chenbopeng/Harmonic_GOTO_equator/doc/主控板PCB.jpg

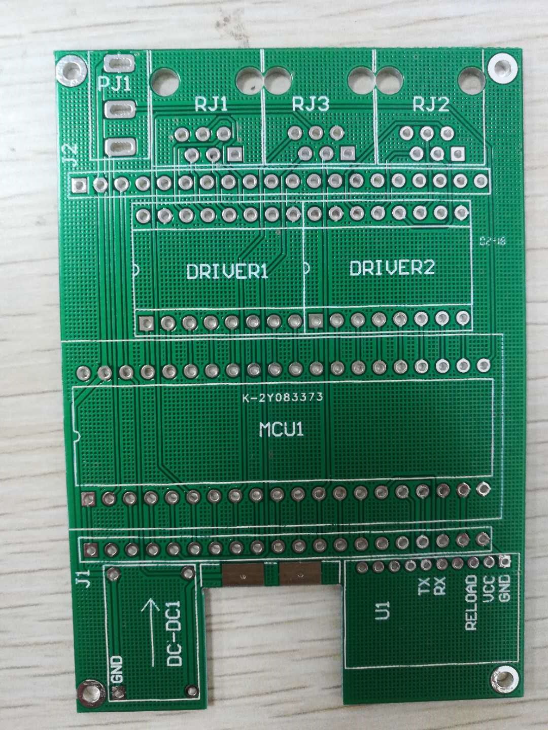
doc/主控板PCB.jpg
