chenbopeng/Harmonic_GOTO_equator/doc/主控板正面 (2).jpg

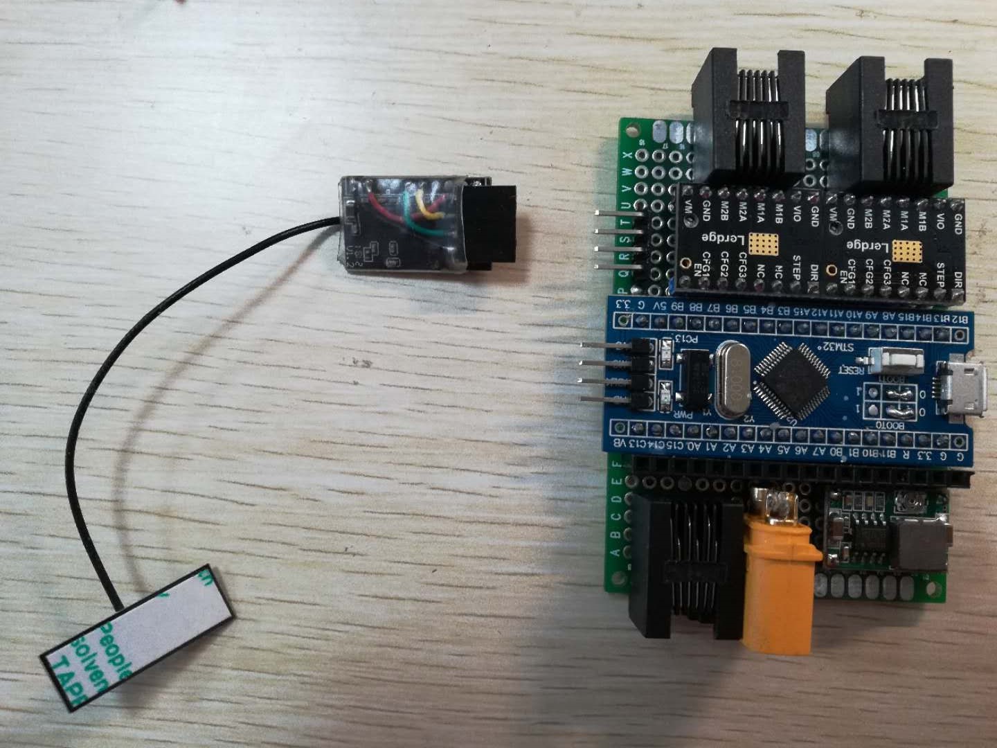
doc/主控板正面 (2).jpg
