chenbopeng/Harmonic_GOTO_equator/doc/按键板PCB.jpg

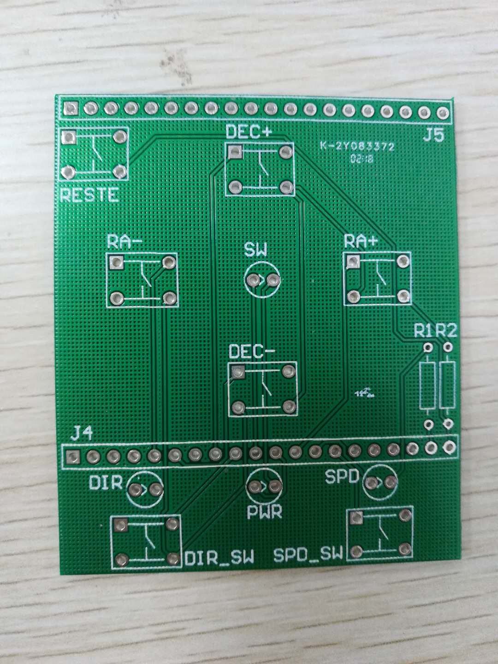
doc/按键板PCB.jpg
