chenbopeng/Harmonic_GOTO_equator/doc/虚拟串口设置.jpg

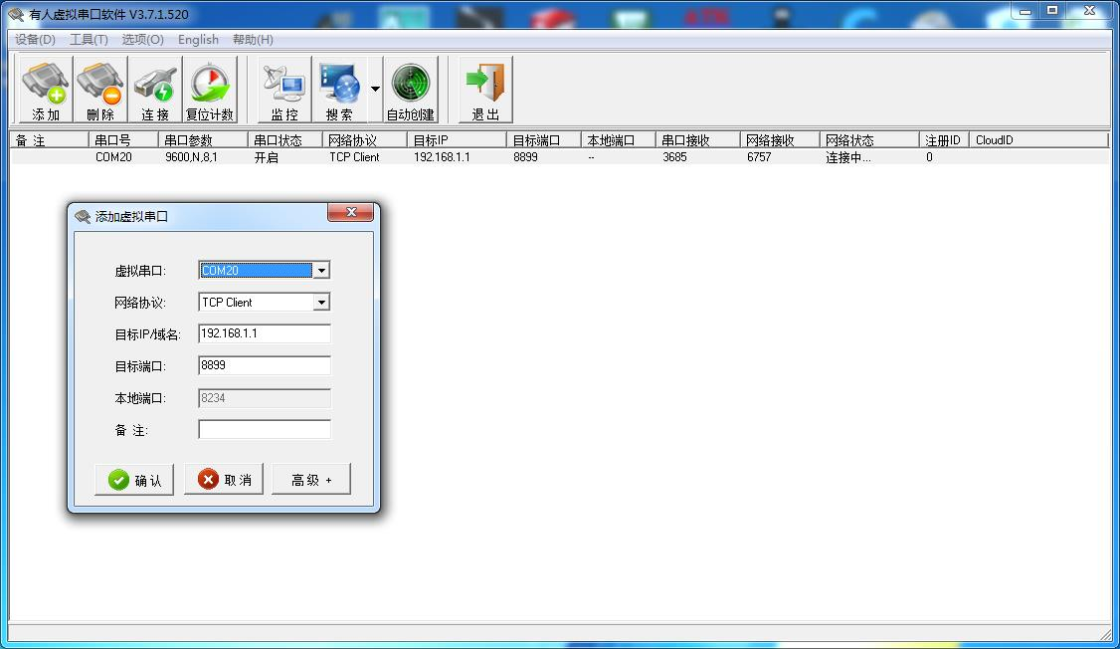
doc/虚拟串口设置.jpg
