chenbopeng/Harmonic_GOTO_equator/mach/热靴导星镜/T7C摄像头.SLDPRT

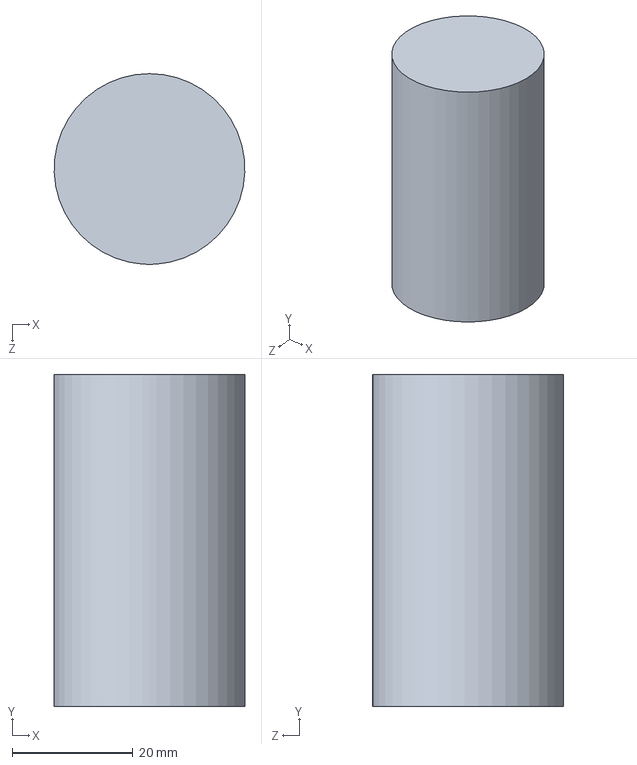
[picture p48: CAD file, 2017-12-30]
mach/热靴导星镜/T7C摄像头.SLDPRT
31.6 x 55.0 x 31.6 mm
