chenbopeng/Harmonic_GOTO_equator/mach/第四版外壳盖.sldprt

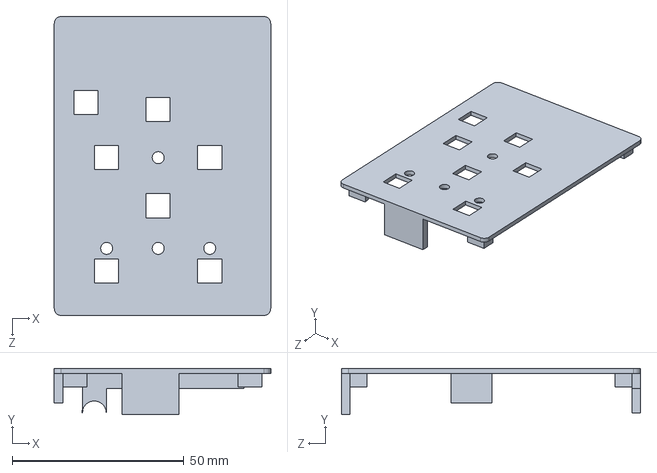
[picture p49: CAD file, 2018-05-16]
mach/第四版外壳盖.sldprt
63.0 x 13.5 x 87.0 mm
