chenbopeng/Harmonic_GOTO_equator/mach/SK10光轴支架.SLDPRT

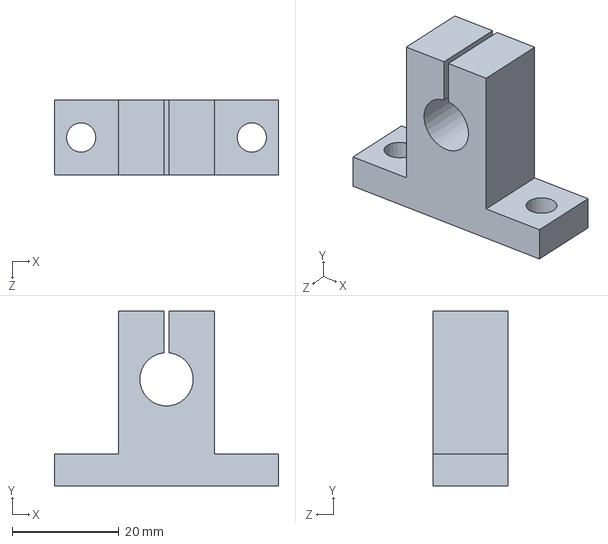
[picture p50: CAD file, 2018-01-17]
mach/SK10光轴支架.SLDPRT
42.0 x 32.8 x 14.0 mm
