chenbopeng/Harmonic_GOTO_equator/mach/热靴导星镜/mini导星镜抱箍.SLDPRT

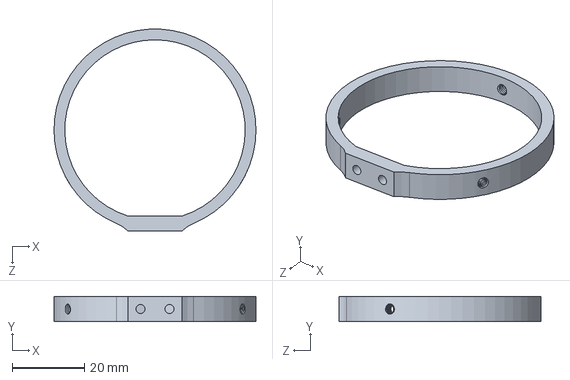
[picture p51: CAD file, 2017-12-30]
mach/热靴导星镜/mini导星镜抱箍.SLDPRT
56.0 x 7.00 x 56.0 mm
