chenbopeng/Harmonic_GOTO_equator/mach/第四版外壳底.sldprt

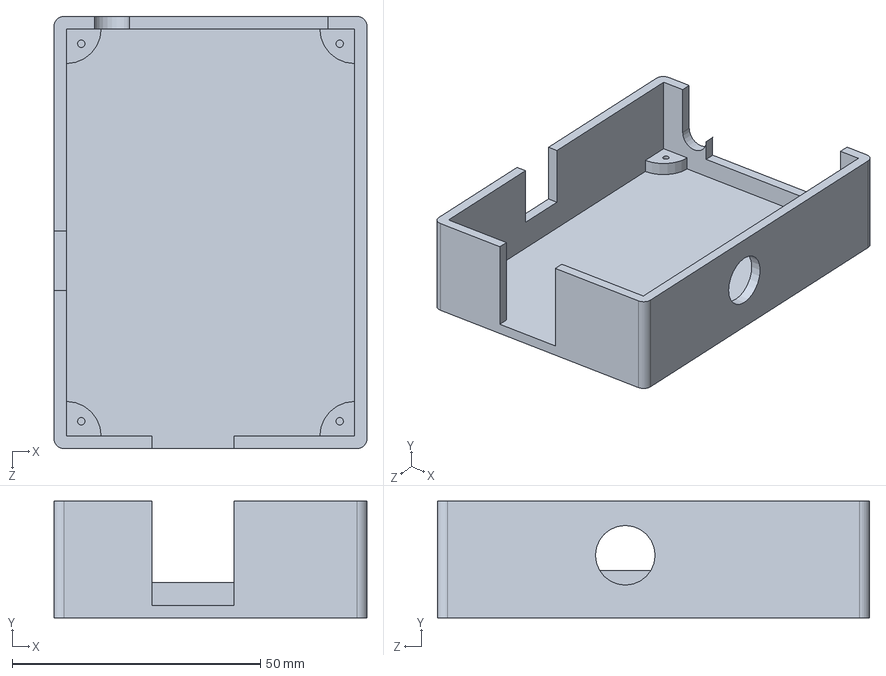
[picture p52: CAD file, 2018-01-15]
mach/第四版外壳底.sldprt
63.0 x 23.5 x 87.0 mm
