chenbopeng/Harmonic_GOTO_equator/mach/热靴导星镜/T7C抱箍.SLDPRT

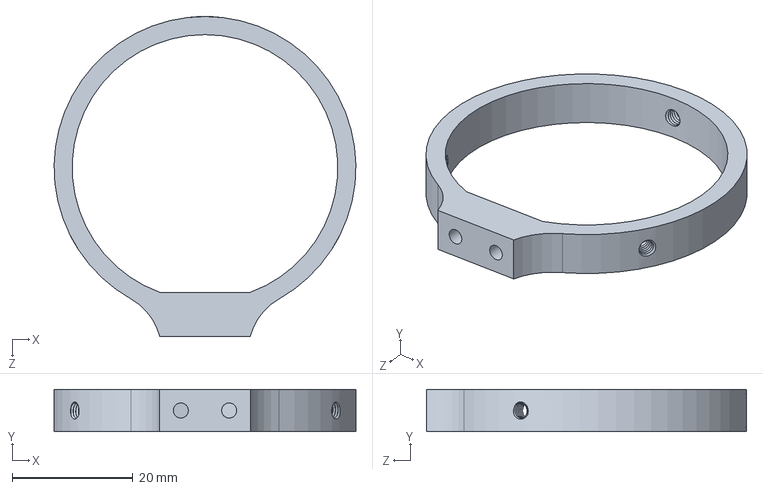
[picture p53: CAD file, 2017-12-30]
mach/热靴导星镜/T7C抱箍.SLDPRT
50.0 x 7.00 x 53.0 mm
