chenbopeng/Harmonic_GOTO_equator/mach/重锤连接件.SLDPRT

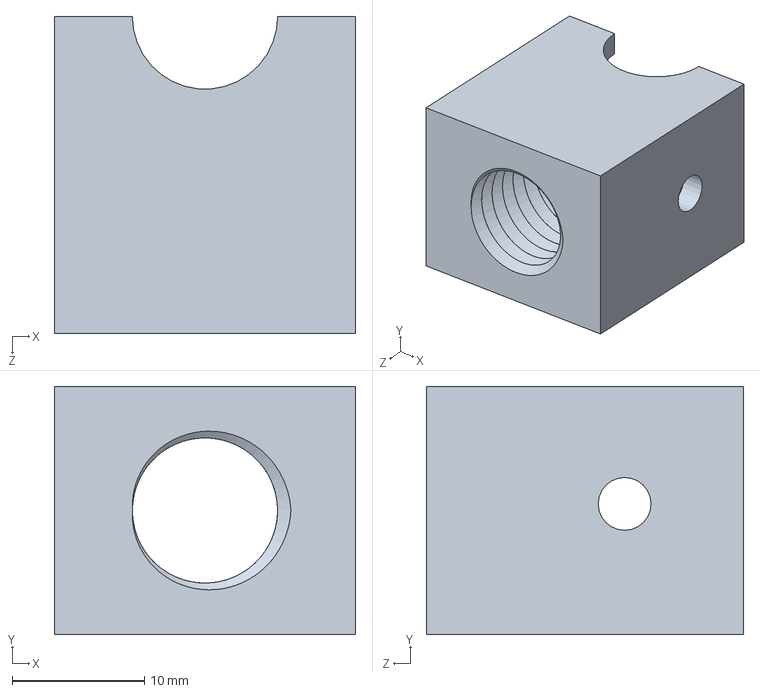
[picture p54: CAD file, 2017-12-30]
mach/重锤连接件.SLDPRT
22.8 x 18.8 x 24.0 mm
