chenbopeng/Harmonic_GOTO_equator/mach/谐波减速电机安装座.SLDPRT

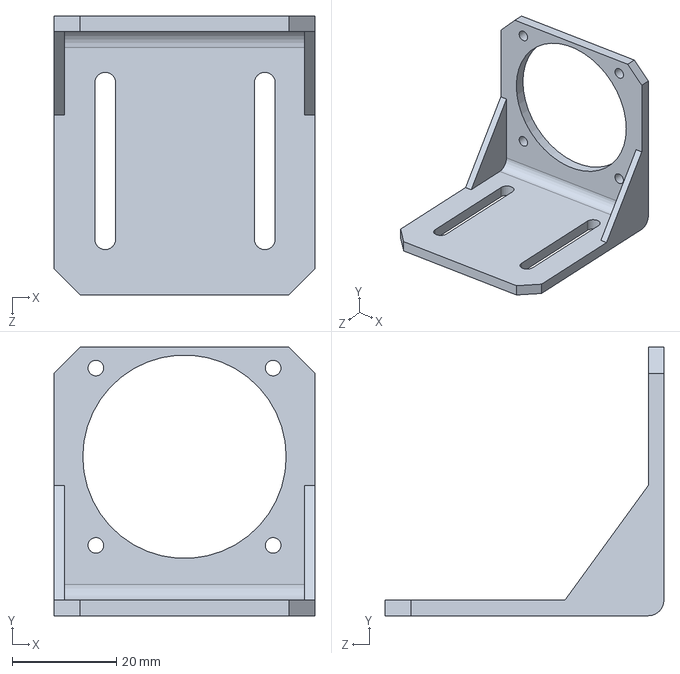
[picture p55: CAD file, 2017-12-30]
mach/谐波减速电机安装座.SLDPRT
50.0 x 51.5 x 53.5 mm
