chenbopeng/Harmonic_GOTO_equator/mach/重锤杆.SLDPRT

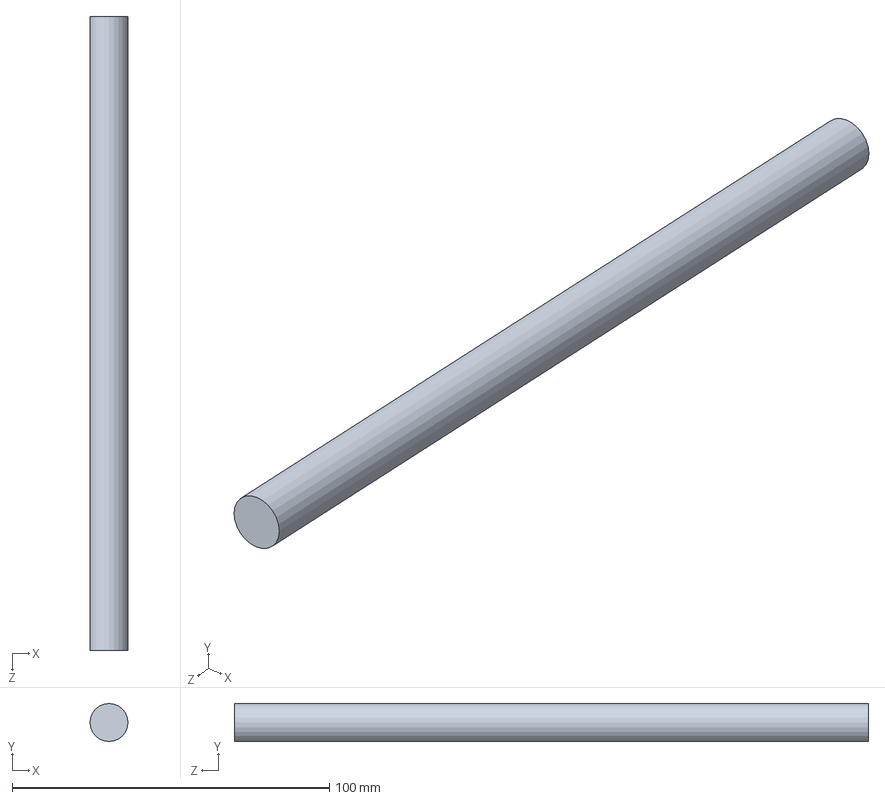
[picture p56: CAD file, 2017-12-30]
mach/重锤杆.SLDPRT
12.0 x 12.0 x 200.0 mm
