chenbopeng/Harmonic_GOTO_equator/mach/球台转接座.SLDPRT

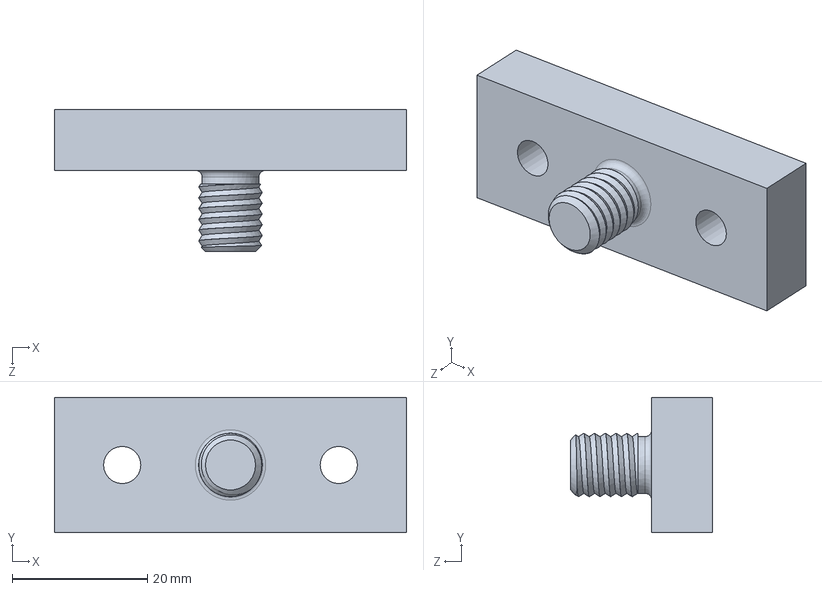
[picture p57: CAD file, 2017-12-30]
mach/球台转接座.SLDPRT
52.0 x 20.0 x 21.0 mm
