chenbopeng/Harmonic_GOTO_equator/mach/斜劈20度.SLDPRT

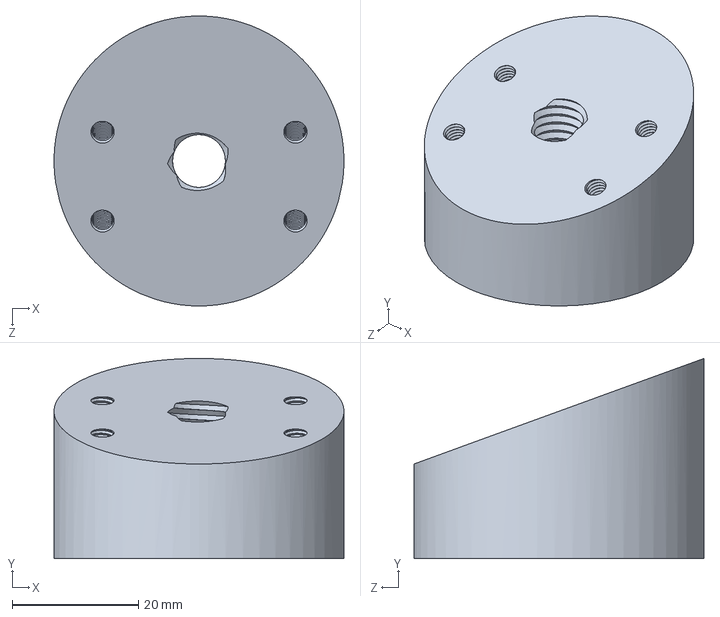
[picture p58: CAD file, 2017-12-30]
mach/斜劈20度.SLDPRT
46.0 x 31.7 x 46.0 mm
