chenbopeng/Harmonic_GOTO_equator/mach/增高节P50.SLDPRT

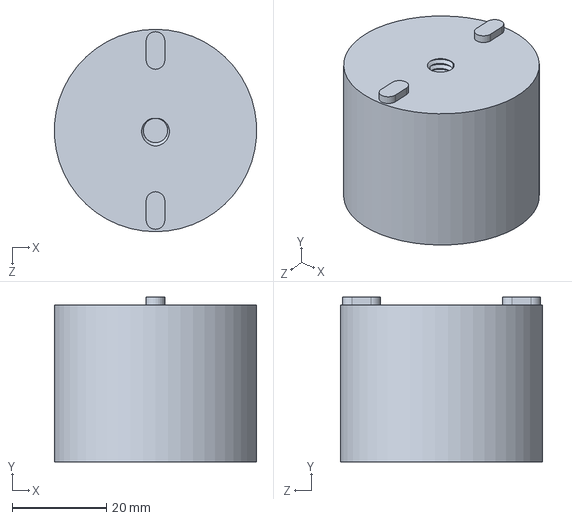
[picture p59: CAD file, 2017-12-30]
mach/增高节P50.SLDPRT
42.9 x 35.0 x 43.0 mm
