chenbopeng/Harmonic_GOTO_equator/mach/SHF10光轴支架.SLDPRT

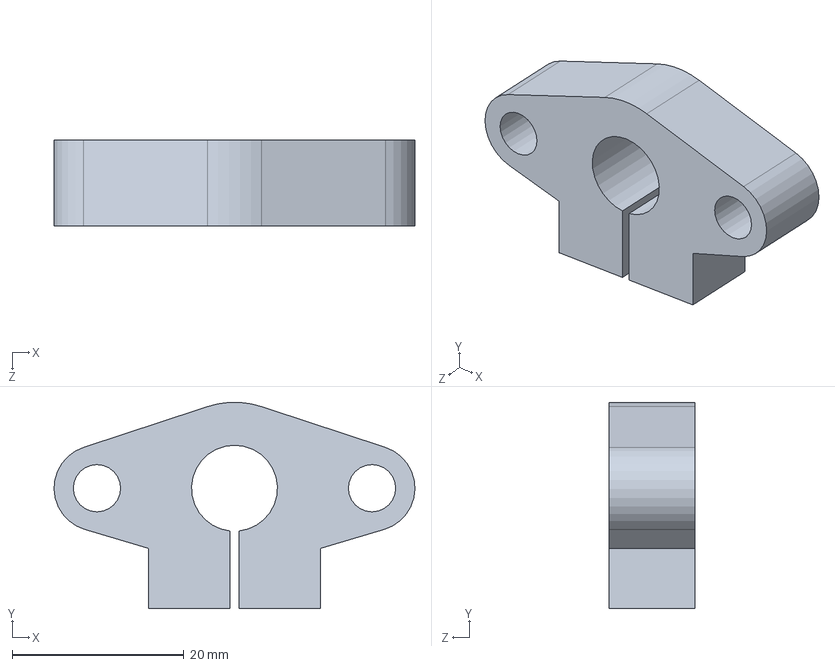
[picture p60: CAD file, 2017-12-30]
mach/SHF10光轴支架.SLDPRT
42.0 x 24.0 x 10.0 mm
