chenbopeng/Harmonic_GOTO_equator/mach/球台活动球.SLDPRT

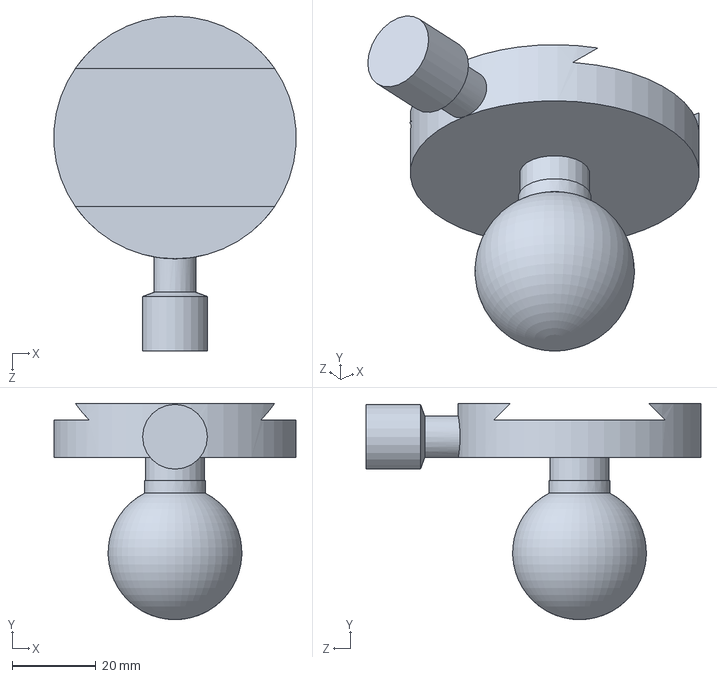
[picture p61: CAD file, 2017-12-30]
mach/球台活动球.SLDPRT
57.9 x 51.7 x 80.0 mm
