chenbopeng/Harmonic_GOTO_equator/mach/斜劈22度.SLDPRT

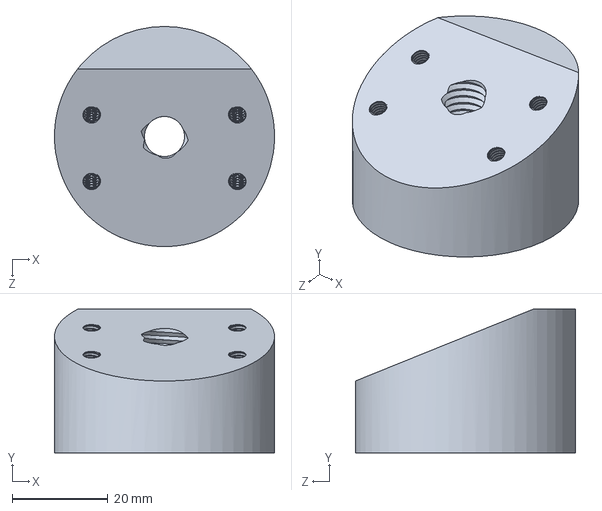
[picture p62: CAD file, 2017-12-30]
mach/斜劈22度.SLDPRT
46.0 x 30.0 x 46.0 mm
