chenbopeng/Harmonic_GOTO_equator/mach/激光安装座.SLDPRT

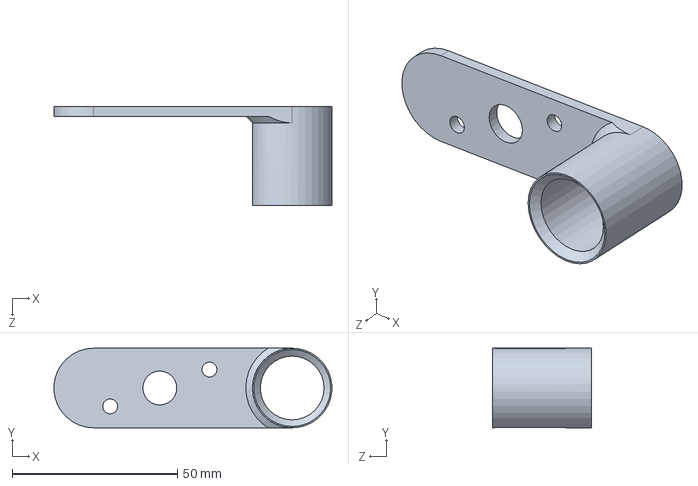
[picture p63: CAD file, 2017-12-30]
mach/激光安装座.SLDPRT
84.0 x 24.0 x 30.0 mm
