chenbopeng/Harmonic_GOTO_equator/mach/第三版外壳盖.SLDPRT

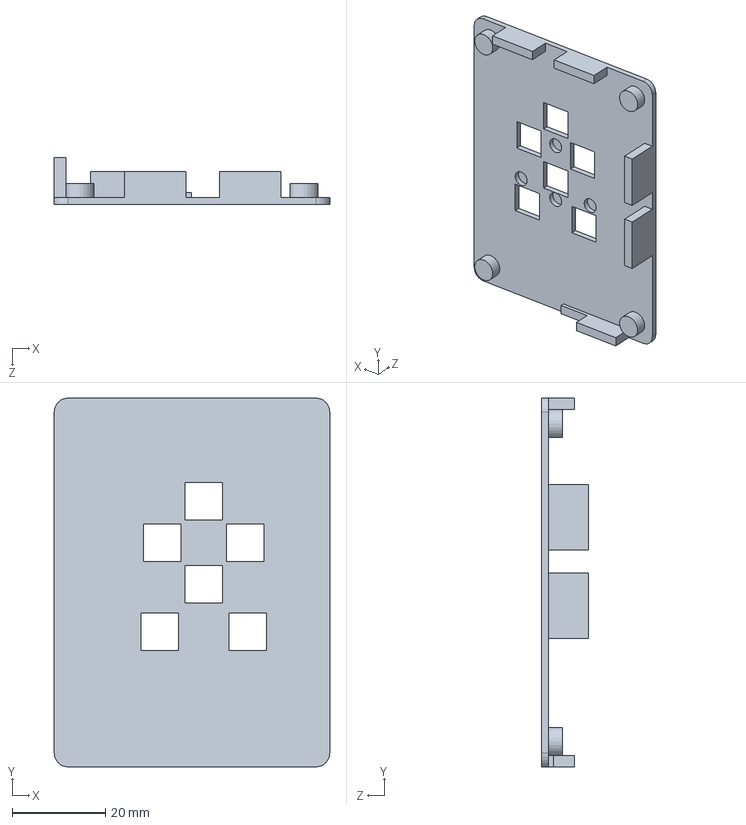
[picture p64: CAD file, 2017-12-30]
mach/第三版外壳盖.SLDPRT
59.0 x 79.0 x 10.0 mm
