chenbopeng/Harmonic_GOTO_equator/mach/第三版外壳底.SLDPRT

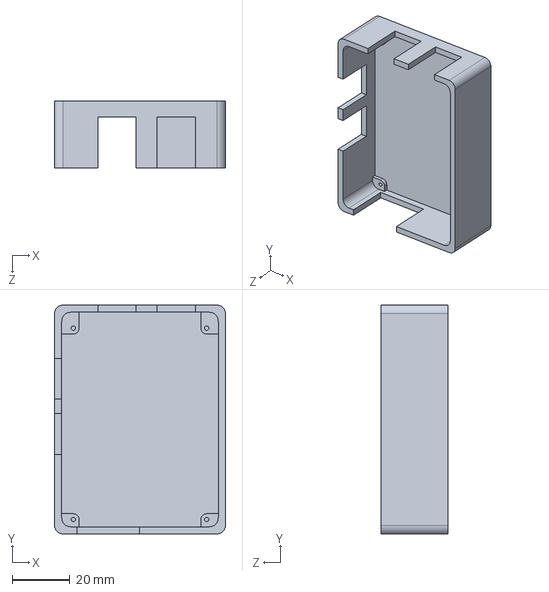
[picture p65: CAD file, 2017-12-30]
mach/第三版外壳底.SLDPRT
59.0 x 79.0 x 23.0 mm
