chenbopeng/Harmonic_GOTO_equator/mach/100减速比谐波减速42步进电机.SLDPRT

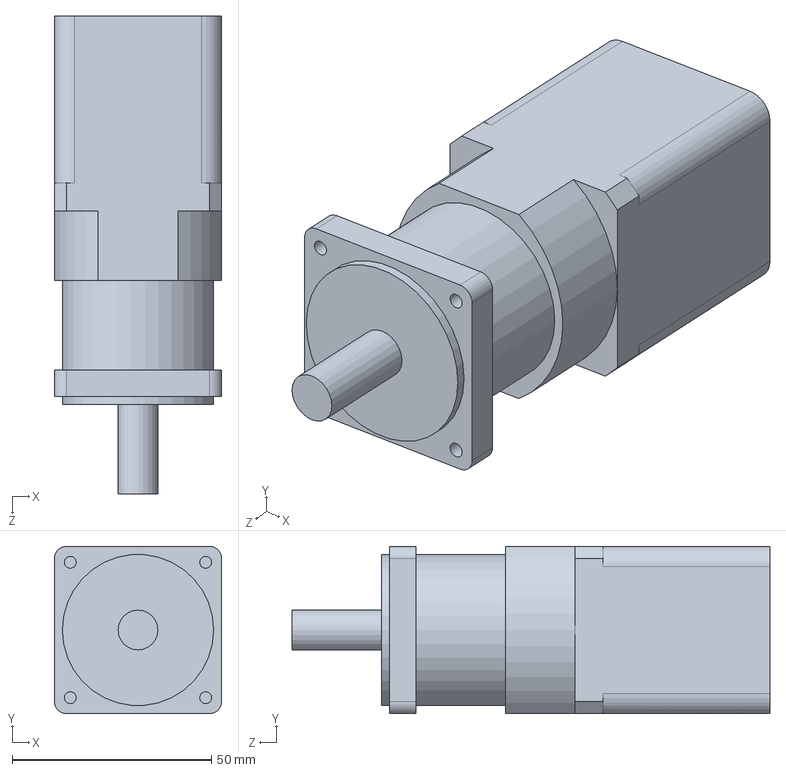
[picture p66: CAD file, 2017-12-30]
mach/100减速比谐波减速42步进电机.SLDPRT
42.0 x 42.0 x 120.1 mm
