chenbopeng/Harmonic_GOTO_equator/mach/K50云台板.SLDPRT

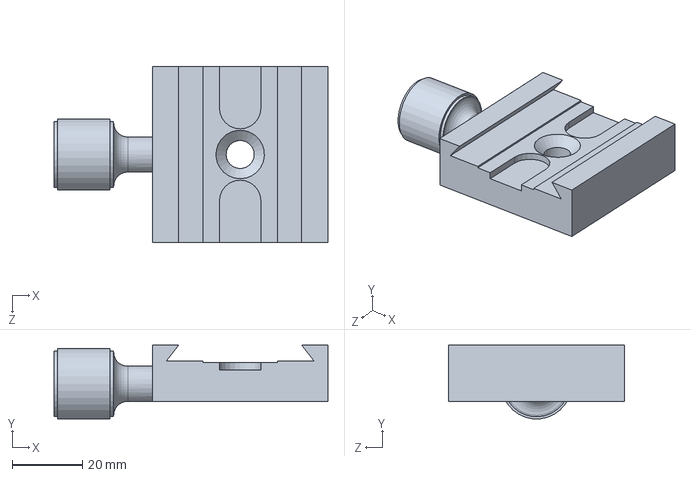
[picture p67: CAD file, 2017-12-30]
mach/K50云台板.SLDPRT
78.0 x 21.0 x 50.0 mm
