chenbopeng/Harmonic_GOTO_equator/mach/球台转接座3D打印.SLDPRT

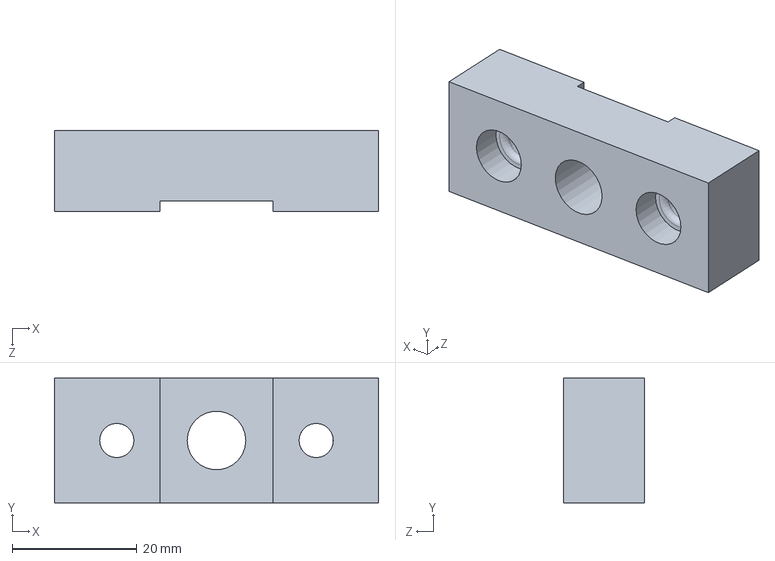
[picture p68: CAD file, 2017-12-30]
mach/球台转接座3D打印.SLDPRT
52.0 x 20.0 x 13.0 mm
