chenbopeng/Harmonic_GOTO_equator/mach/斜劈32度.SLDPRT

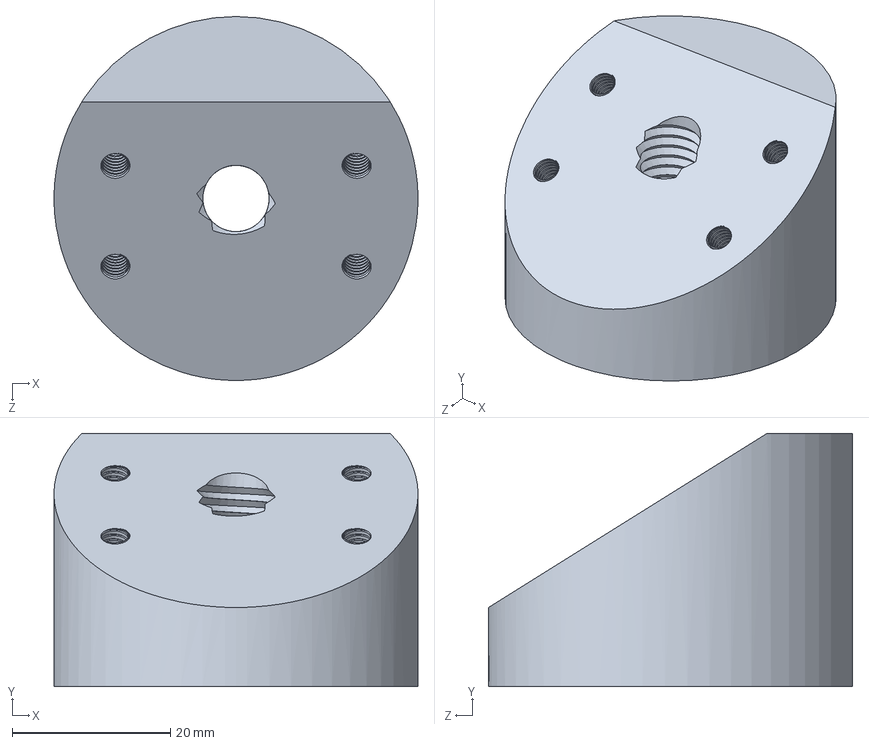
[picture p69: CAD file, 2017-12-30]
mach/斜劈32度.SLDPRT
46.0 x 32.0 x 46.0 mm
