chenbopeng/Harmonic_GOTO_equator/mach/球台底座.SLDPRT

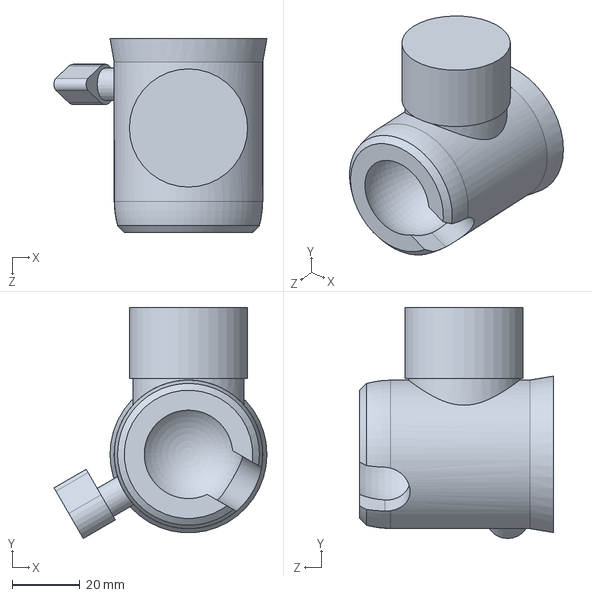
[picture p70: CAD file, 2017-12-30]
mach/球台底座.SLDPRT
63.1 x 68.4 x 57.5 mm
