chenbopeng/Harmonic_GOTO_equator/src/SYSTEM/usart/usart.c

#include "sys.h"
#include "usart.h"
////////////////////////////////////////////////////////////////////////////////// 	 
#if SYSTEM_SUPPORT_OS
#include "includes.h"					//ucos 使用	  
#endif

#if 1
#pragma import(__use_no_semihosting)             
//标准库需要的支持函数                 
struct __FILE 
{ 
	int handle; 

}; 

FILE __stdout;       
//定义_sys_exit()以避免使用半主机模式    
_sys_exit(int x) 
{ 
	x = x; 
} 
//重定义fputc函数 
int fputc(int ch, FILE *f)
{      
	while((USART3->SR&0X40)==0);//循环发送,直到发送完毕   
    USART3->DR = (u8) ch;      
	return ch;
}
#endif 

#if EN_USART1_RX   //如果使能了接收
//串口1中断服务程序
//注意,读取USARTx->SR能避免莫名其妙的错误   	
u8 USART_RX_BUF[USART_REC_LEN];     //接收缓冲,最大USART_REC_LEN个字节.
//接收状态
//bit15，	接收完成标志
//bit14，	接收到0x0d
//bit13~0，	接收到的有效字节数目
u16 USART_RX_STA=0;       //接收状态标记	  
  
void uart1_init(u32 bound){
  //GPIO端口设置
  GPIO_InitTypeDef GPIO_InitStructure;
	USART_InitTypeDef USART_InitStructure;
	NVIC_InitTypeDef NVIC_InitStructure;
	 
	RCC_APB2PeriphClockCmd(RCC_APB2Periph_USART1|RCC_APB2Periph_GPIOA, ENABLE);	//使能USART1，GPIOA时钟
  
	//USART1_TX   GPIOA.9
  GPIO_InitStructure.GPIO_Pin = GPIO_Pin_9; //PA.9
  GPIO_InitStructure.GPIO_Speed = GPIO_Speed_50MHz;
  GPIO_InitStructure.GPIO_Mode = GPIO_Mode_AF_PP;	//复用推挽输出
  GPIO_Init(GPIOA, &GPIO_InitStructure);//初始化GPIOA.9
   
  //USART1_RX	  GPIOA.10初始化
  GPIO_InitStructure.GPIO_Pin = GPIO_Pin_10;//PA10
  GPIO_InitStructure.GPIO_Mode = GPIO_Mode_IN_FLOATING;//浮空输入
  GPIO_Init(GPIOA, &GPIO_InitStructure);//初始化GPIOA.10  

  //Usart1 NVIC 配置
  NVIC_InitStructure.NVIC_IRQChannel = USART1_IRQn;
	NVIC_InitStructure.NVIC_IRQChannelPreemptionPriority=3 ;//抢占优先级3
	NVIC_InitStructure.NVIC_IRQChannelSubPriority = 3;		//子优先级3
	NVIC_InitStructure.NVIC_IRQChannelCmd = ENABLE;			//IRQ通道使能
	NVIC_Init(&NVIC_InitStructure);	//根据指定的参数初始化VIC寄存器
  
   //USART 初始化设置

	USART_InitStructure.USART_BaudRate = bound;//串口波特率
	USART_InitStructure.USART_WordLength = USART_WordLength_8b;//字长为8位数据格式
	USART_InitStructure.USART_StopBits = USART_StopBits_1;//一个停止位
	USART_InitStructure.USART_Parity = USART_Parity_No;//无奇偶校验位
	USART_InitStructure.USART_HardwareFlowControl = USART_HardwareFlowControl_None;//无硬件数据流控制
	USART_InitStructure.USART_Mode = USART_Mode_Rx | USART_Mode_Tx;/*| USART_Mode_Tx;*/	//收发模式
  USART_Init(USART1, &USART_InitStructure); //初始化串口1
	
//  USART_ITConfig(USART1, USART_IT_RXNE, ENABLE);//开启串口接受中断
	USART_ITConfig(USART1, USART_IT_IDLE, ENABLE);  //IDLE IT enable
	USART_DMACmd(USART1,USART_DMAReq_Rx,ENABLE);   //DMA enable
  USART_Cmd(USART1, ENABLE);                    //使能串口1 

}

void DMA_init(u32 buffer,u16 size)
{
	DMA_InitTypeDef DMA_InitStructure;
 	RCC_AHBPeriphClockCmd(RCC_AHBPeriph_DMA1, ENABLE);	//使能DMA传输
	
  DMA_DeInit(DMA1_Channel3);   //将DMA的通道1寄存器重设为缺省值
	DMA_InitStructure.DMA_PeripheralBaseAddr = (u32)(&USART3->DR);  //DMA外设ADC基地址
	DMA_InitStructure.DMA_MemoryBaseAddr = buffer;  //DMA内存基地址
	DMA_InitStructure.DMA_DIR = DMA_DIR_PeripheralSRC;  //数据传输方向，从内存读取发送到外设
	DMA_InitStructure.DMA_BufferSize = size;  //DMA通道的DMA缓存的大小
	DMA_InitStructure.DMA_PeripheralInc = DMA_PeripheralInc_Disable;  //外设地址寄存器不变
	DMA_InitStructure.DMA_MemoryInc = DMA_MemoryInc_Enable;  //内存地址寄存器递增
	DMA_InitStructure.DMA_PeripheralDataSize = DMA_PeripheralDataSize_Byte;  //数据宽度为8位
	DMA_InitStructure.DMA_MemoryDataSize = DMA_MemoryDataSize_Byte; //数据宽度为8位
	DMA_InitStructure.DMA_Mode = DMA_Mode_Normal;  //工作在正常缓存模式
	DMA_InitStructure.DMA_Priority = DMA_Priority_Medium; //DMA通道 x拥有中优先级 
	DMA_InitStructure.DMA_M2M = DMA_M2M_Disable;  //DMA通道x没有设置为内存到内存传输
	DMA_Init(DMA1_Channel3, &DMA_InitStructure);  //根据DMA_InitStruct中指定的参数初始化DMA的通道USART1_Tx_DMA_Channel所标识的寄存器
	DMA_Cmd(DMA1_Channel3,ENABLE);	
	
} 

void uart3_init(u32 bound){
	
  //GPIO端口设置
  GPIO_InitTypeDef GPIO_InitStructure;
	USART_InitTypeDef USART_InitStructure;
	NVIC_InitTypeDef NVIC_InitStructure;
	 
	RCC_APB1PeriphClockCmd(RCC_APB1Periph_USART3, ENABLE);	//使能USART1，GPIOA时钟
  RCC_APB2PeriphClockCmd(RCC_APB2Periph_GPIOB, ENABLE);
	//USART1_TX   GPIOA.9
  GPIO_InitStructure.GPIO_Pin = GPIO_Pin_10; //PA.9
  GPIO_InitStructure.GPIO_Speed = GPIO_Speed_50MHz;
  GPIO_InitStructure.GPIO_Mode = GPIO_Mode_AF_PP;	//复用推挽输出
  GPIO_Init(GPIOB, &GPIO_InitStructure);//初始化GPIOA.9
   
  //USART1_RX	  GPIOA.10初始化
  GPIO_InitStructure.GPIO_Pin = GPIO_Pin_11;//PA10
  GPIO_InitStructure.GPIO_Mode = GPIO_Mode_IN_FLOATING;//浮空输入
  GPIO_Init(GPIOB, &GPIO_InitStructure);//初始化GPIOA.10  
	
	//Usart1 NVIC 配置
  NVIC_InitStructure.NVIC_IRQChannel = USART3_IRQn;
	NVIC_InitStructure.NVIC_IRQChannelPreemptionPriority=3 ;//抢占优先级3
	NVIC_InitStructure.NVIC_IRQChannelSubPriority = 3;		//子优先级3
	NVIC_InitStructure.NVIC_IRQChannelCmd = ENABLE;			//IRQ通道使能
	NVIC_Init(&NVIC_InitStructure);	//根据指定的参数初始化VIC寄存器
  
	USART_InitStructure.USART_BaudRate = bound;//串口波特率
	USART_InitStructure.USART_WordLength = USART_WordLength_8b;//字长为8位数据格式
	USART_InitStructure.USART_StopBits = USART_StopBits_1;//一个停止位
	USART_InitStructure.USART_Parity = USART_Parity_No;//无奇偶校验位
	USART_InitStructure.USART_HardwareFlowControl = USART_HardwareFlowControl_None;//无硬件数据流控制
	USART_InitStructure.USART_Mode = USART_Mode_Rx | USART_Mode_Tx;	//收发模式

  USART_Init(USART3, &USART_InitStructure); //初始化串口1
	
  USART_ITConfig(USART3, USART_IT_IDLE, ENABLE);//开启串idle中断
	USART_DMACmd(USART3,USART_DMAReq_Rx,ENABLE);   //DMA enable
	USART_DMACmd(USART3,USART_DMAReq_Tx,ENABLE); 
  USART_Cmd(USART3, ENABLE);                    //使能串口1 
}

extern u8 data_receive_buffer[USART_REC_LEN] ;

void USART3_IRQHandler(void)                	//串口1中断服务程序
	{
		if ( USART_GetITStatus(USART3,USART_IT_IDLE) != RESET )
		{
      data_receive_buffer[USART_REC_LEN-1] = USART3->SR;
			data_receive_buffer[USART_REC_LEN-1] = USART3->DR; //USART_IT_IDLE clear
			data_receive_buffer[USART_REC_LEN-1] = 1;
			DMA_Cmd(DMA1_Channel3,DISABLE);
			DMA_SetCurrDataCounter(DMA1_Channel3,USART_REC_LEN);  //reset size
			DMA_Cmd(DMA1_Channel3,ENABLE);
		}
	} 

#endif	
