chenbopeng/Harmonic_GOTO_equator/src/HARDWARE/KEY/key.c

#include "key.h"
#include "delay.h"

//按键初始化函数 
//PA15和PC5 设置成输入
void KEY_Init(void)
{
	GPIO_InitTypeDef GPIO_InitStructure;

 	RCC_APB2PeriphClockCmd(RCC_APB2Periph_GPIOA,ENABLE);//使能PORTA,PORTC时钟

	GPIO_InitStructure.GPIO_Pin  = GPIO_Pin_1;//PA1
	GPIO_InitStructure.GPIO_Mode = GPIO_Mode_IPU; //设置成上拉输入
 	GPIO_Init(GPIOA, &GPIO_InitStructure);//初始化GPIOA15
	
	GPIO_InitStructure.GPIO_Pin  = GPIO_Pin_2;//PA2
	GPIO_InitStructure.GPIO_Mode = GPIO_Mode_IPU; //设置成上拉输入
 	GPIO_Init(GPIOA, &GPIO_InitStructure);//初始化GPIOC5
 
	GPIO_InitStructure.GPIO_Pin  = GPIO_Pin_3;//PA3
	GPIO_InitStructure.GPIO_Mode = GPIO_Mode_IPU; //PA0设置成输入，默认下拉	  
	GPIO_Init(GPIOA, &GPIO_InitStructure);//初始化GPIOA.0
	
	GPIO_InitStructure.GPIO_Pin  = GPIO_Pin_4;//PA4
	GPIO_InitStructure.GPIO_Mode = GPIO_Mode_IPU; //PA0设置成输入，默认下拉	  
	GPIO_Init(GPIOA, &GPIO_InitStructure);//初始化GPIOA.0
} 
//按键处理函数
//返回按键值
//mode:0,不支持连续按;1,支持连续按;
//返回值：
//0，没有任何按键按下
//KEY0_PRES，KEY0按下
//KEY1_PRES，KEY1按下
//WKUP_PRES，WK_UP按下 
//注意此函数有响应优先级,KEY0>KEY1>WK_UP!!

//u8 KEY_Scan(u8 mode)
//{	 
//	static u8 key_up=1;//按键按松开标志
//	if(mode)key_up=1;  //支持连按		  
//	if(key_up&&(KEY0==0||KEY1==0||WK_UP==1))
//	{
//		delay_ms(10);//去抖动 
//		key_up=0;
//		if(KEY0==0)return KEY0_PRES;
//		else if(KEY1==0)return KEY1_PRES;
//		else if(WK_UP==1)return WKUP_PRES; 
//	}else if(KEY0==1&&KEY1==1&&WK_UP==0)key_up=1; 	     
//	return 0;// 无按键按下
//}
