chenbopeng/Harmonic_GOTO_equator/src/HARDWARE/PWM/pwm.c

#include "pwm.h"
//PWM输出初始化
//arr：自动重装值
//psc：时钟预分频数
void TIM_PWM_Init(u16 arr,u16 psc)
{  
	GPIO_InitTypeDef GPIO_InitStructure;
	TIM_TimeBaseInitTypeDef  TIM_TimeBaseStructure;
	TIM_OCInitTypeDef  TIM_OCInitStructure;

	RCC_APB2PeriphClockCmd(RCC_APB2Periph_GPIOB|RCC_APB2Periph_GPIOC,ENABLE);
	RCC_APB1PeriphClockCmd(RCC_APB1Periph_TIM4,ENABLE); //使能GPIO外设时钟使能
	                                                                     	
	GPIO_InitStructure.GPIO_Pin=GPIO_Pin_8|GPIO_Pin_9;    //使用B8.9
	GPIO_InitStructure.GPIO_Speed=GPIO_Speed_50MHz;
	GPIO_InitStructure.GPIO_Mode=GPIO_Mode_AF_PP;
	GPIO_Init(GPIOB,&GPIO_InitStructure);
	
	TIM_TimeBaseStructure.TIM_Period = arr; //设置在下一个更新事件装入活动的自动重装载寄存器周期的值	 80K
	TIM_TimeBaseStructure.TIM_Prescaler =psc; //设置用来作为TIMx时钟频率除数的预分频值  不分频
	TIM_TimeBaseStructure.TIM_ClockDivision = 0; //设置时钟分割:TDTS = Tck_tim
	TIM_TimeBaseStructure.TIM_CounterMode = TIM_CounterMode_Up;  //TIM向上计数模式
	TIM_TimeBaseStructure.TIM_RepetitionCounter=0x00;
	TIM_TimeBaseInit(TIM4, &TIM_TimeBaseStructure); //根据TIM_TimeBaseInitStruct中指定的参数初始化TIMx的时间基数单位

	TIM_OCInitStructure.TIM_OCMode = TIM_OCMode_PWM1; //选择定时器模式:TIM脉冲宽度调制模式2
	TIM_OCInitStructure.TIM_OutputState = TIM_OutputState_Enable; //比较输出使能
	TIM_OCInitStructure.TIM_OCPolarity = TIM_OCPolarity_High; //输出极性:TIM输出比较极性高
 
	TIM_OCInitStructure.TIM_Pulse=21600;
	TIM_OC3Init(TIM4,&TIM_OCInitStructure); 

	TIM_OCInitStructure.TIM_Pulse=21600;
	TIM_OC4Init(TIM4,&TIM_OCInitStructure); 
		
  TIM_CtrlPWMOutputs(TIM4,ENABLE);	//MOE 主输出使能	

	TIM_Cmd(TIM4, ENABLE);  //使能TIM1
 
}
